somekindofnate/cadre/src/IMG_0206.jpg

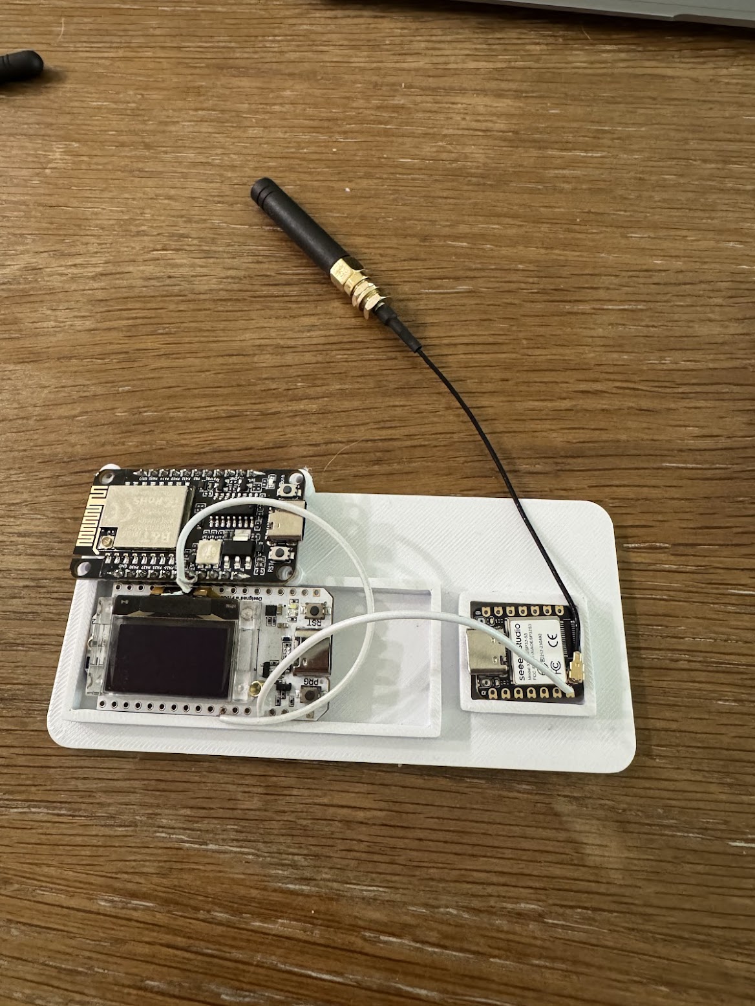
src/IMG_0206.jpg
