somekindofnate/cadre/src/IMG_0207.jpg

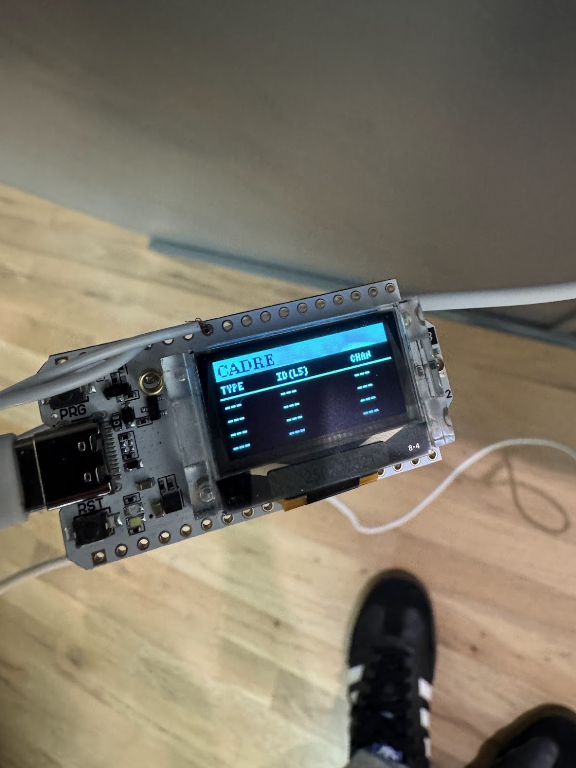
src/IMG_0207.jpg
